c0ff33-dev/nand2tetris-fpga/08_3D_Printer/00_Dev_Jig/Images/07_Final.jpg

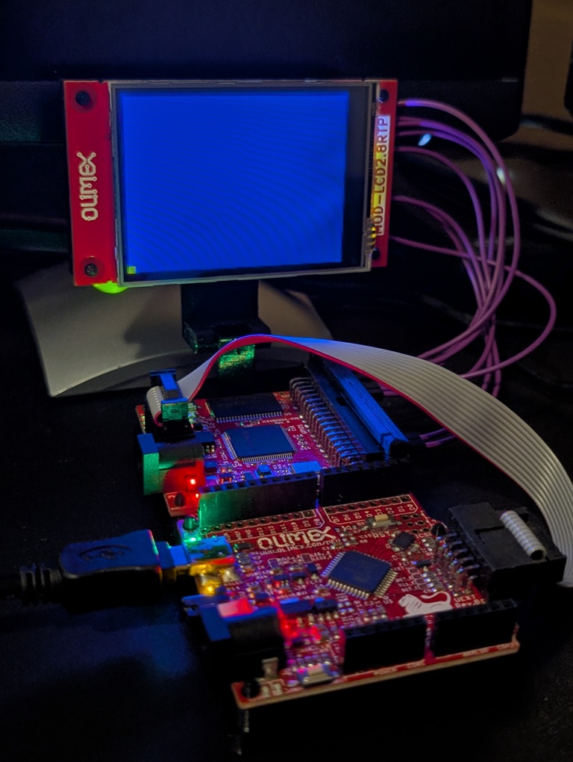
08_3D_Printer/00_Dev_Jig/Images/07_Final.jpg
