c0ff33-dev/nand2tetris-fpga/09_More_Fun_to_Go/01_IO_Devices/01_SRAM_Tests/Readme.md

# 01 SRAM Tests

Additional tests for debugging SRAM implementation and the boot/run mode transition.
