c0ff33-dev/nand2tetris-fpga/09_More_Fun_to_Go/02_Operating_System/07_String_Test/Readme.md

# 07 String Test

- Replaced `Main.jack` with original nand2tetris implementation using `Output` class instead of `StdIO`.
- Upload: `cd ~/src/nand2tetris-fpga/09_More_Fun_to_Go/02_Operating_System/07_String_Test && make && make upload`
