c0ff33-dev/nand2tetris-fpga/09_More_Fun_to_Go/02_Operating_System/14_Keyboard_Test/Readme.md

# 14 Keyboard Test

- No changes from original nand2tetris course implementation.
- Upload: `cd ~/src/nand2tetris-fpga/09_More_Fun_to_Go/02_Operating_System/14_Keyboard_Test && make && make upload`
