c0ff33-dev/nand2tetris-fpga/09_More_Fun_to_Go/00_HACK/Include.v

`include "../../01_Boolean_Logic/Nand.v"
`include "../../01_Boolean_Logic/Not.v"
`include "../../01_Boolean_Logic/Buffer.v"
`include "../../01_Boolean_Logic/And.v"
`include "../../01_Boolean_Logic/Or.v"
`include "../../01_Boolean_Logic/Xor.v"
`include "../../01_Boolean_Logic/Mux.v"
`include "../../01_Boolean_Logic/DMux.v"
`include "../../01_Boolean_Logic/Not16.v"
`include "../../01_Boolean_Logic/Buffer16.v"
`include "../../01_Boolean_Logic/And16.v"
`include "../../01_Boolean_Logic/Or16.v"
`include "../../01_Boolean_Logic/Mux16.v"
`include "../../01_Boolean_Logic/Or8Way.v"
`include "../../01_Boolean_Logic/Mux4Way16.v"
`include "../../01_Boolean_Logic/Mux8Way16.v"
`include "../../01_Boolean_Logic/DMux4Way.v"
`include "../../01_Boolean_Logic/DMux8Way.v"

`include "../../02_Boolean_Arithmetic/HalfAdder.v"
`include "../../02_Boolean_Arithmetic/FullAdder.v"
`include "../../02_Boolean_Arithmetic/Add16.v"
`include "../../02_Boolean_Arithmetic/Inc16.v"
`include "../../02_Boolean_Arithmetic/ALU.v"

`include "../../03_Sequential_Logic/DFF.v"
`include "../../03_Sequential_Logic/Bit.v"
`include "../../03_Sequential_Logic/Register.v"
`include "../../03_Sequential_Logic/PC.v"
`include "../../03_Sequential_Logic/RAM256.v"
`include "../../03_Sequential_Logic/RAM512.v"
`include "../../03_Sequential_Logic/RAM3584.v"
`include "../../03_Sequential_Logic/BitShift9R.v"
`include "../../03_Sequential_Logic/BitShift8L.v"

`include "../../05_Computer_Architecture/CPU.v"
`include "../../05_Computer_Architecture/ROM.v"

`include "../../06_IO_Devices/SPI.v"
`include "../../06_IO_Devices/InOut.v"
`include "../../06_IO_Devices/GO.v"

`include "../../09_More_Fun_to_Go/Clock25_Reset20.v"
`include "../../09_More_Fun_to_Go/HACK.v"
`include "../../09_More_Fun_to_Go/Memory.v"
`include "../../09_More_Fun_to_Go/SRAM_D.v"
`include "../../09_More_Fun_to_Go/01_IO_Devices/Keyboard.v"
`include "../../09_More_Fun_to_Go/01_IO_Devices/PS2.v"
`include "../../09_More_Fun_to_Go/01_IO_Devices/VGA.v"
