c0ff33-dev/nand2tetris-fpga/01_Boolean_Logic/00_Nand/Nand_tb.v

`default_nettype none
module Nand_tb();
    
    // IN,OUT
    reg a,b;
    wire out;

    // Part
    Nand NAND(
        .a(a),
        .b(b),
        .out(out)
    );

    // Compare
    wire out_cmp;
    assign out_cmp = ~(a&b);
    
    reg fail = 0;
    task check;
        #1
        if (out != out_cmp) 
            begin
                $display("FAIL: a=%1b, b=%1b, out=%1b",a,b,out);
                fail=1;
            end
    endtask
      
    // Test    
    initial begin
        $dumpfile("Nand_tb.vcd");
        $dumpvars(0, Nand_tb);
        
        $display("------------------------");
        $display("Test bench: Nand");
        
        a=0;b=0;check();
        a=0;b=1;check();
        a=1;b=0;check();
        a=1;b=1;check();
            
        if (fail==0) $display("passed");
        $display("------------------------");
        $finish;
    end

endmodule
