c0ff33-dev/nand2tetris-fpga/06_IO_Devices/03_SPI/SPI_tb.v

`timescale 10ns/1ns
`default_nettype none

module SPI_tb();

    // IN,OUT
    reg clk = 0;
    reg load = 0;
    reg [15:0] in = 0;
    wire [15:0] out;
    wire CSX;
    wire SDO;
    reg SDI=0;
    wire SCK;

    // Part
    SPI SPI(
        .clk(clk),
        .load(load),
        .in(in),
        .out(out),
        .CSX(CSX),
        .SDO(SDO),
        .SDI(SDI),
        .SCK(SCK)
    );
    
    // Simulate
    always #2 clk=~clk; // 25 MHz
    wire trigger;
    assign trigger = (n==9) || (n==18) || (n==27) || (n==40);
    always @(posedge clk) begin
        // send 2 random bytes with CSX=0, 1 byte with CSX=1, 1 random byte
        case ({trigger, (n >= 9), ((n >= 27) & (n < 40))})
            2'b10: in <= 16'h000 | ($random & 8'hFF);
            2'b11: in <= 16'h100 | ($random & 8'hFF);
            default: in <= $random;
        endcase
        load <= trigger;
        SDI <= $random;
    end

    // Compare
    reg[4:0] bits=0;
    always @(negedge clk) // counter
        // if load & in[8]=0 bits=1 (new byte)
        // else if bits=8 reset, else if busy bits++ else bits=0
        bits <= (load&~in[8])?1:((bits==8)?0:(busy?bits+1:0));
    wire busy=|bits; // busy if bits>0
    wire [15:0] out_cmp = {busy,7'd0,shift};
    reg [7:0] shift=0;
    reg miso_s;
    always @(posedge SCK)
        miso_s <= SDI;
    always @(negedge clk)
        shift <= load?in[7:0]:((busy&~clk)?{shift[6:0],miso_s}:shift);
    wire SCK_cmp=busy&clk;
    reg CSX_cmp=1;
    always @(posedge clk) begin
        if (trigger)
            CSX_cmp <= 1'b0; // drive low on load
        else
            CSX_cmp<=load?in[8]:CSX_cmp;
    end
    wire SDO_cmp=shift[7] & busy;
    reg fail = 0;
    reg [31:0] n = 0;
    task check;
        #4
        if ((out!=out_cmp)||(SCK!=SCK_cmp)||(SDO!=SDO_cmp)||(CSX!=CSX_cmp))
            begin
                $display("FAIL: clk=%1b, load=%1b, in=%16b, out=%16b, CSX=%1b, SDO=%1b, SDI=%1b, SCK=%1b",clk,load,in,out,CSX,SDO,SDI,SCK);
                fail=1;
            end
    endtask

    initial begin
        $dumpfile("SPI_tb.vcd");
        $dumpvars(0, SPI_tb);
        
        $display("------------------------");
        $display("Test bench: SPI");

        for (n=0; n<400;n=n+1) 
                check();
        
        if (fail==0) $display("passed");
        $display("------------------------");
        $finish;
    end

endmodule
