c0ff33-dev/nand2tetris-fpga/06_IO_Devices/04_SRAM/SRAM_D_tb.v

`timescale 10ns/1ns
`default_nettype none

module SRAM_D_tb();

    // IN,OUT
    reg clk = 0;
    reg load = 0;
    reg [15:0] in=0;
    wire [15:0] out;
    wire CSX;
    wire OEX;
    wire WEX;
    wire [15:0] DATA;

    // Part
    SRAM_D SRAM_D(
        .clk(clk),
        .load(load),
        .in(in),
        .out(out),
        .CSX(CSX),
        .OEX(OEX),
        .WEX(WEX),
        .DATA(DATA)
    );
    
    // Simulate
    always #2 clk=~clk; // 25 MHz
    wire trigger;
    reg write=0;
    assign trigger = (n==4) || (n==8) || (n==12) || (n==16) || (n==20);
    always @(posedge clk) begin
        in <= $random;
        load <= trigger;
        write <= load;
    end
    reg [15:0] DATA_cmp = 16'bzzzzzzzzzzzzzzzz;
    reg [15:0] out_cmp = 16'bzzzzzzzzzzzzzzzz;
    always @(posedge clk)
        if (load) DATA_cmp <= in;
    always @(negedge clk)
        out_cmp <= (~CSX_cmp&~OEX_cmp)?16'bzzzzzzzzzzzzzzzz:DATA_cmp; 
    // Compare
    wire CSX_cmp = 0;
    wire OEX_cmp = write;
    wire WEX_cmp = ~write;
    reg fail = 0;
    reg [31:0] n = 0;
    task check;
        #4
        if ((out!=out_cmp)||(DATA!=DATA_cmp)||(CSX!=CSX_cmp)||(OEX!=OEX_cmp)||(WEX!=WEX_cmp))
            begin
                $display("FAIL: clk=%1b, load=%1b, in=%16b, out=%16b, CSX=%1b, OEX=%1b, SEX=%1b, DATA=%16b",clk,load,in,out,CSX,OEX,WEX,DATA);
                fail=1;
            end
    endtask

    initial begin
        $dumpfile("SRAM_D_tb.vcd");
        $dumpvars(0, SRAM_D_tb);
        
        $display("------------------------");
        $display("Test bench: SRAM_D");

        for (n=0; n<24;n=n+1) 
                check();
        
        if (fail==0) $display("passed");
        $display("------------------------");
        $finish;
    end

endmodule
