c0ff33-dev/nand2tetris-fpga/06_IO_Devices/05_GO/GO_tb.v

`timescale 10ns/1ns
`default_nettype none

module GO_tb();

    // IN,OUT
    reg clk = 0;
    reg load = 0;
    reg [15:0] sram_addr=0;
    reg [15:0] pc=0;
    wire [15:0] SRAM_ADDR;
    reg [15:0] rom_data=0;
    reg [15:0] sram_data=0;
    wire [15:0] instruction;
    wire [15:0] out;

    // Part
    GO GO(
        .clk(clk),
        .load(load),
        .sram_addr_in(sram_addr),
        .pc(pc),
        .sram_addr_out(SRAM_ADDR),
        .rom_data(rom_data),
        .sram_data(sram_data),
        .instruction(instruction),
        .out(out)
    );
    
    // Simulate
    always #2 clk=~clk; // 25 MHz
    wire trigger;
    reg write;
    assign trigger = (n==10);
    always @(posedge clk) begin
        sram_addr <= $random;
        pc <= $random;
        rom_data <= $random;
        sram_data <= $random;
        load <= trigger;
    end
    
    // Compare
    reg fail = 0;
    reg [31:0] n = 0;
    reg [15:0] run=0;
    always @(posedge clk)
        if (load) run <=1;
    wire [15:0] SRAM_ADDR_cmp=run?pc:sram_addr;
    wire [15:0] instruction_cmp=run?sram_data:rom_data;
    task check;
        #4
        if ((SRAM_ADDR!=SRAM_ADDR_cmp) || (instruction!=instruction_cmp) || (out!=run))
            begin
                $display("FAIL: clk=%1b, load=%1b",clk,load);
                fail=1;
            end
    endtask

    initial begin
        $dumpfile("GO_tb.vcd");
        $dumpvars(0, GO_tb);
        
        $display("------------------------");
        $display("Test bench: GO");

        for (n=0; n<20;n=n+1) 
                check();
        
        if (fail==0) $display("passed");
        $display("------------------------");
        $finish;
    end

endmodule
